lore95/DataFusion/src/DataFusionExe/PressureReadings/project/regressions/V1_40_128.png

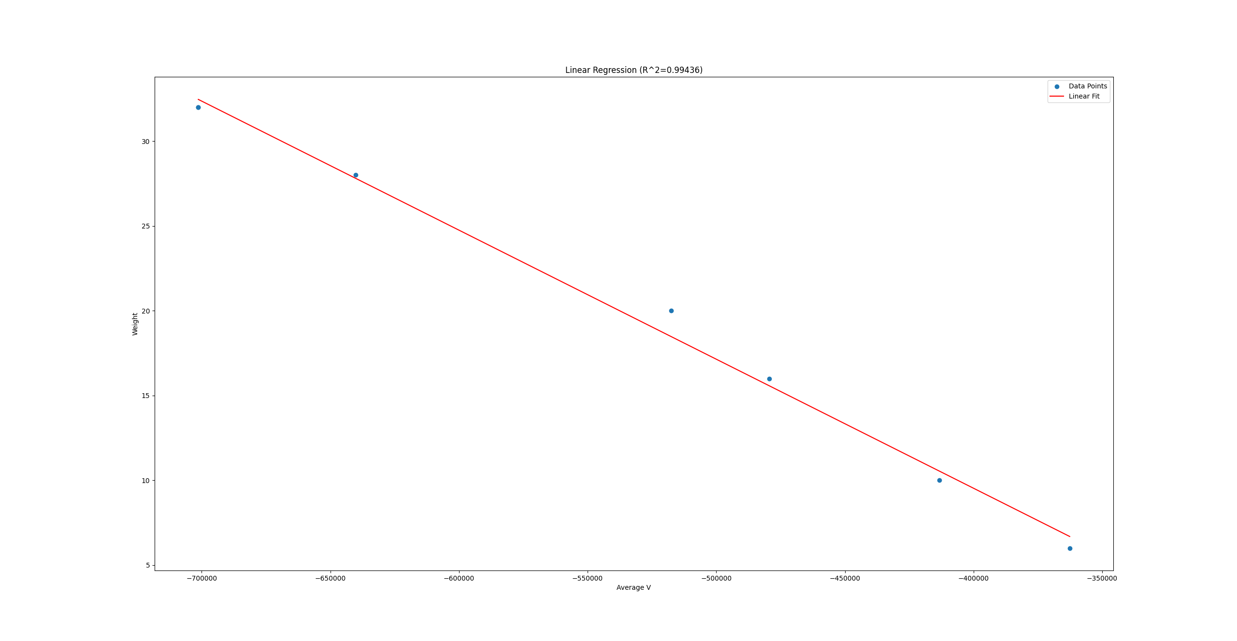
src/DataFusionExe/PressureReadings/project/regressions/V1_40_128.png
